TallesSantosCUBoulder/EIT-Capstone-Project-2023/EIT_MATLAB_Test/EIT FFT Test.jpg

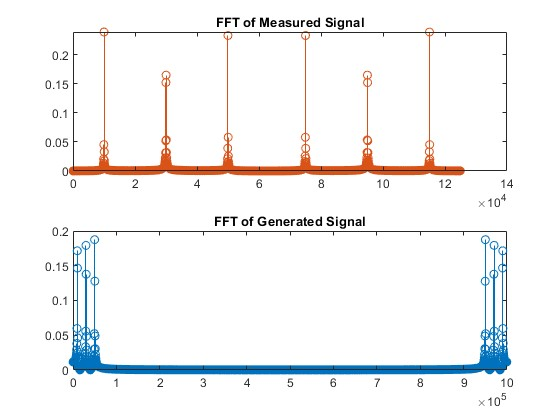
EIT_MATLAB_Test/EIT FFT Test.jpg
