TallesSantosCUBoulder/EIT-Capstone-Project-2023/Howland_Circuit_Design/LTSpice/howlandDrM_double.asc

Cn1: cap; 1µ
Cn2: cap; 1µ
Cp1: cap; 1µ
Cp2: cap; 1µ
LOADn: res; 1k
LOADp: res; 1k
OPn: AD8066
OPp: AD8066
Rin1: res; 100k
Rin2: res; 100k
Rin3: res; 100k
Rin4: res; 100k
Rn1: res; 47k
Rn2: res; 47k
Rn3: res; 47k
Rn4: res; 47k
Rn5: res; 1k
Rp1: res; 47k
Rp2: res; 47k
Rp3: res; 47k
Rp4: res; 47k
Rp5: res; 1k
U1: AD8137
V1: voltage; 12
V2: voltage; 12
V3: voltage; 1v
V4: voltage; SINE(0 .5 125k)
Named nets: 0, +V, -V, V+, V-, V1
200 to 2k Ohms
.tran 0 .00004 0 .000004
200 to 2k Ohms
1Vpp
