TallesSantosCUBoulder/EIT-Capstone-Project-2023/Howland_Circuit_Design/LTSpice/howlandDrM_single.asc

BODY: res; 2000
C1: cap; 1µ
C2: cap; 1µ
R1: res; 47k
R2: res; 47k
R3: res; 47k
R4: res; 47k
R5: res; 1k
U1: AD8066
V1: voltage; 12
V2: voltage; 12
V3: voltage; SINE(0 .5 125k)
Named nets: 0, +V, -V, Vin
200 to 2k Ohms
.tran 0 .00004 0 .000004
1Vpp
